DavoliLuca/embedded_system_design/mplabx/stepper_motor.h

/* Microchip Technology Inc. and its subsidiaries.  You may use this software 
 * and any derivatives exclusively with Microchip products. 
 * 
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
 * IN NO EVENT WILL MICROCHIP BE LIABLE FOR ANY INDIRECT, SPECIAL, PUNITIVE, 
 * INCIDENTAL OR CONSEQUENTIAL LOSS, DAMAGE, COST OR EXPENSE OF ANY KIND 
 * WHATSOEVER RELATED TO THE SOFTWARE, HOWEVER CAUSED, EVEN IF MICROCHIP HAS 
 * BEEN ADVISED OF THE POSSIBILITY OR THE DAMAGES ARE FORESEEABLE.  TO THE 
 * FULLEST EXTENT ALLOWED BY LAW, MICROCHIP'S TOTAL LIABILITY ON ALL CLAIMS 
 * IN ANY WAY RELATED TO THIS SOFTWARE WILL NOT EXCEED THE AMOUNT OF FEES, IF 
 * ANY, THAT YOU HAVE PAID DIRECTLY TO MICROCHIP FOR THIS SOFTWARE.
 *
 * MICROCHIP PROVIDES THIS SOFTWARE CONDITIONALLY UPON YOUR ACCEPTANCE OF THESE 
 * TERMS. 
 */

/* 
 * File:   
 * Author: 
 * Comments:
 * Revision history: 
 */

// This is a guard condition so that contents of this file are not included
// more than once.  
#ifndef XC_HEADER_TEMPLATE_H
#define	XC_HEADER_TEMPLATE_H

#include <xc.h> // include processor files - each processor file is guarded.  

// TODO Insert appropriate #include <>

// TODO Insert C++ class definitions if appropriate

// TODO Insert declarations

// Comment a function and leverage automatic documentation with slash star star
/**
    <p><b>Function prototype:</b></p>
  
    <p><b>Summary:</b></p>

    <p><b>Description:</b></p>

    <p><b>Precondition:</b></p>

    <p><b>Parameters:</b></p>

    <p><b>Returns:</b></p>

    <p><b>Example:</b></p>
    <code>
 
    </code>

    <p><b>Remarks:</b></p>
 */
// TODO Insert declarations or function prototypes (right here) to leverage 
// live documentation

#ifdef	__cplusplus
extern "C" {
#endif /* __cplusplus */

    // TODO If C++ is being used, regular C code needs function names to have C 
    // linkage so the functions can be used by the c code. 

#ifdef	__cplusplus
}
#endif /* __cplusplus */

#endif	/* XC_HEADER_TEMPLATE_H */

#define COILS_NUMBER 4

typedef struct {
    int current_coil;
    int step_counter;
    int direction;
    unsigned char hex_coil_register_values[COILS_NUMBER];
    volatile unsigned char* register_name;
} stepperMotor;

void turn_on_current_coil(stepperMotor* stepper_motor);
void init_stepper(stepperMotor* stepper_motor, int current_step, int step_counter, int direction, unsigned char hex_coil_register_values[COILS_NUMBER], volatile unsigned char *register_name);
void update_current_coil(stepperMotor* stepper_motor);
int reach_goal(stepperMotor* stepper_motor, int goal_to_reach);
void change_direction(stepperMotor* stepper_motor);
