DavoliLuca/embedded_system_design/mplabx/init_PIC.c

// PIC18F452 Configuration Bit Settings

// 'C' source line config statements

// CONFIG1H
#pragma config OSC = RCIO       // Oscillator Selection bits (RC oscillator w/ OSC2 configured as RA6)
#pragma config OSCS = OFF       // Oscillator System Clock Switch Enable bit (Oscillator system clock switch option is disabled (main oscillator is source))

// CONFIG2L
#pragma config PWRT = OFF       // Power-up Timer Enable bit (PWRT disabled)
#pragma config BOR = ON         // Brown-out Reset Enable bit (Brown-out Reset enabled)
#pragma config BORV = 20        // Brown-out Reset Voltage bits (VBOR set to 2.0V)

// CONFIG2H
#pragma config WDT = OFF        // Watchdog Timer Enable bit (WDT disabled (control is placed on the SWDTEN bit))
#pragma config WDTPS = 128      // Watchdog Timer Postscale Select bits (1:128)

// CONFIG3H
#pragma config CCP2MUX = ON     // CCP2 Mux bit (CCP2 input/output is multiplexed with RC1)

// CONFIG4L
#pragma config STVR = ON        // Stack Full/Underflow Reset Enable bit (Stack Full/Underflow will cause RESET)
#pragma config LVP = ON         // Low Voltage ICSP Enable bit (Low Voltage ICSP enabled)

// CONFIG5L
#pragma config CP0 = OFF        // Code Protection bit (Block 0 (000200-001FFFh) not code protected)
#pragma config CP1 = OFF        // Code Protection bit (Block 1 (002000-003FFFh) not code protected)
#pragma config CP2 = OFF        // Code Protection bit (Block 2 (004000-005FFFh) not code protected)
#pragma config CP3 = OFF        // Code Protection bit (Block 3 (006000-007FFFh) not code protected)

// CONFIG5H
#pragma config CPB = OFF        // Boot Block Code Protection bit (Boot Block (000000-0001FFh) not code protected)
#pragma config CPD = OFF        // Data EEPROM Code Protection bit (Data EEPROM not code protected)

// CONFIG6L
#pragma config WRT0 = OFF       // Write Protection bit (Block 0 (000200-001FFFh) not write protected)
#pragma config WRT1 = OFF       // Write Protection bit (Block 1 (002000-003FFFh) not write protected)
#pragma config WRT2 = OFF       // Write Protection bit (Block 2 (004000-005FFFh) not write protected)
#pragma config WRT3 = OFF       // Write Protection bit (Block 3 (006000-007FFFh) not write protected)

// CONFIG6H
#pragma config WRTC = OFF       // Configuration Register Write Protection bit (Configuration registers (300000-3000FFh) not write protected)
#pragma config WRTB = OFF       // Boot Block Write Protection bit (Boot Block (000000-0001FFh) not write protected)
#pragma config WRTD = OFF       // Data EEPROM Write Protection bit (Data EEPROM not write protected)

// CONFIG7L
#pragma config EBTR0 = OFF      // Table Read Protection bit (Block 0 (000200-001FFFh) not protected from Table Reads executed in other blocks)
#pragma config EBTR1 = OFF      // Table Read Protection bit (Block 1 (002000-003FFFh) not protected from Table Reads executed in other blocks)
#pragma config EBTR2 = OFF      // Table Read Protection bit (Block 2 (004000-005FFFh) not protected from Table Reads executed in other blocks)
#pragma config EBTR3 = OFF      // Table Read Protection bit (Block 3 (006000-007FFFh) not protected from Table Reads executed in other blocks)

// CONFIG7H
#pragma config EBTRB = OFF      // Boot Block Table Read Protection bit (Boot Block (000000-0001FFh) not protected from Table Reads executed in other blocks)

// #pragma config statements should precede project file includes.
// Use project enums instead of #define for ON and OFF.

#include <xc.h>
#include "init_PIC.h"

void init_PORTS(void){
    // Init usart and debug led
    LATA = 0;
    PORTA = 0;
    TRISA = 0xF1; // RA0 and RA5 AD conversion so we set them as inputs RA1 output for conv belt
    
    LATB = 0;
    PORTB = 0;
    TRISB = 0x00; // rb0-3 output and the more significant as default on 
   
    // PORTC
    LATC = 0;
    PORTC = 0;
    TRISC = 0x00; // LATC as output 
    TRISCbits.RC7 = 1;  // USART Tx
    
    return;
}

void init_interrupts(void){
    // only interrupt on receiveing a new char
    PIR1bits.RCIF = 0; // clear rcif interrupt flag
    PIE1bits.RCIE = 1; //set rcie interrupt enable
    INTCONbits.PEIE = 1;  //Enable peripherals interrupt
    
    return;
}
